Paul8043/student-bed/docs/bed-stacked.jpg

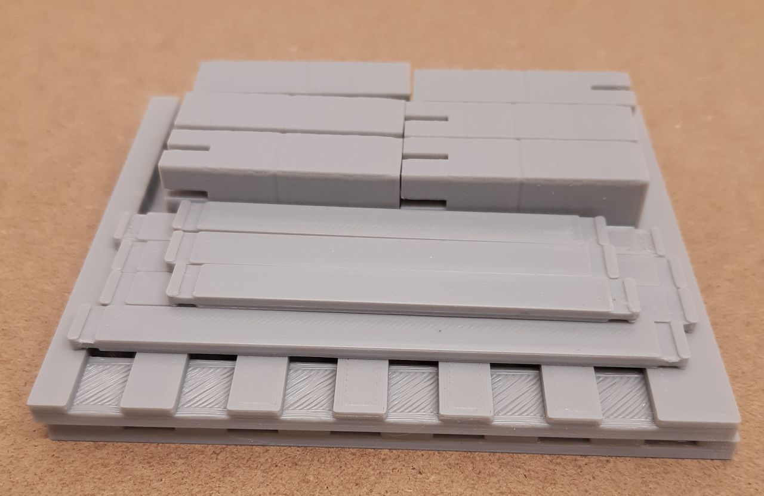
docs/bed-stacked.jpg
