Paul8043/student-bed/docs/duckboard.png

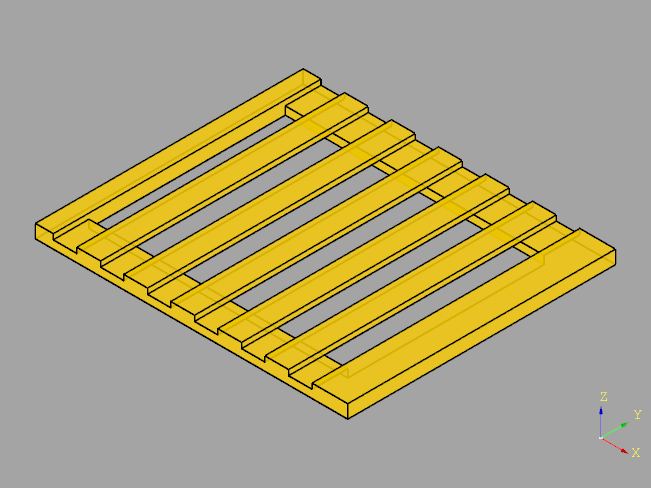
docs/duckboard.png
