Paul8043/student-bed/docs/jamb.png

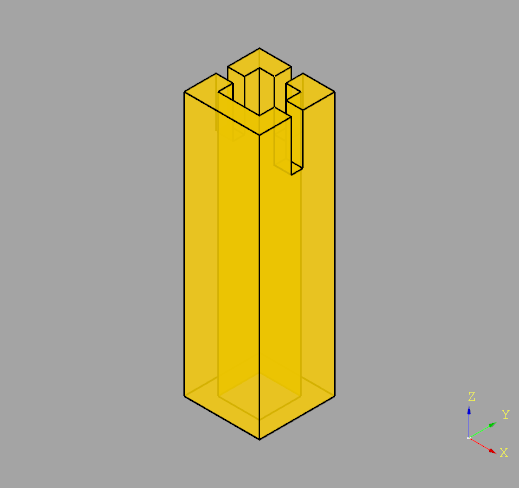
docs/jamb.png
