Paul8043/student-bed/docs/rib.png

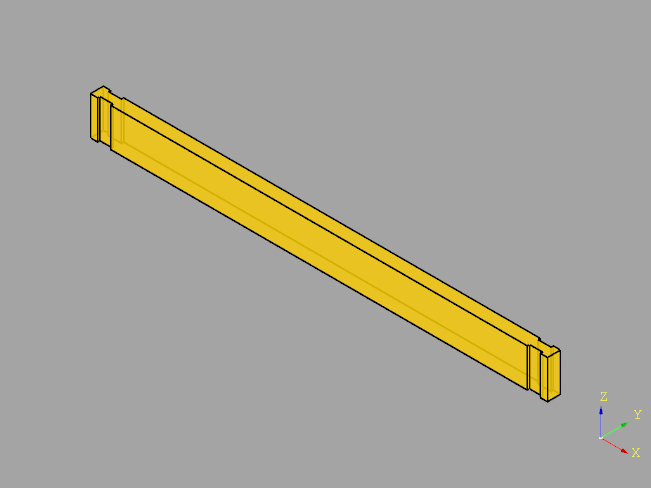
docs/rib.png
