Paul8043/student-bed/docs/parts.png

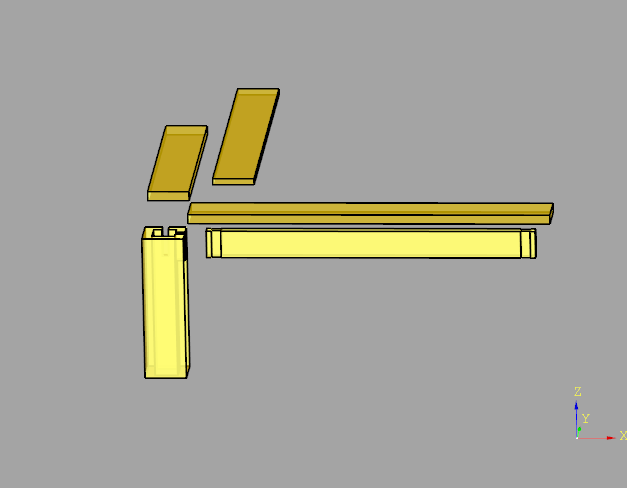
docs/parts.png
